cilynx/onefinity/Calibration/20mm Cube.scad

difference() {
  cube(20);
  translate([2,2,2])
  cube([16,16,20]);
}
