cilynx/onefinity/Hemera/bed_spacers.scad

cube([7.5,32,7.5]);
